TingliangZhang/girlsday2021/image-20210202202509346.png

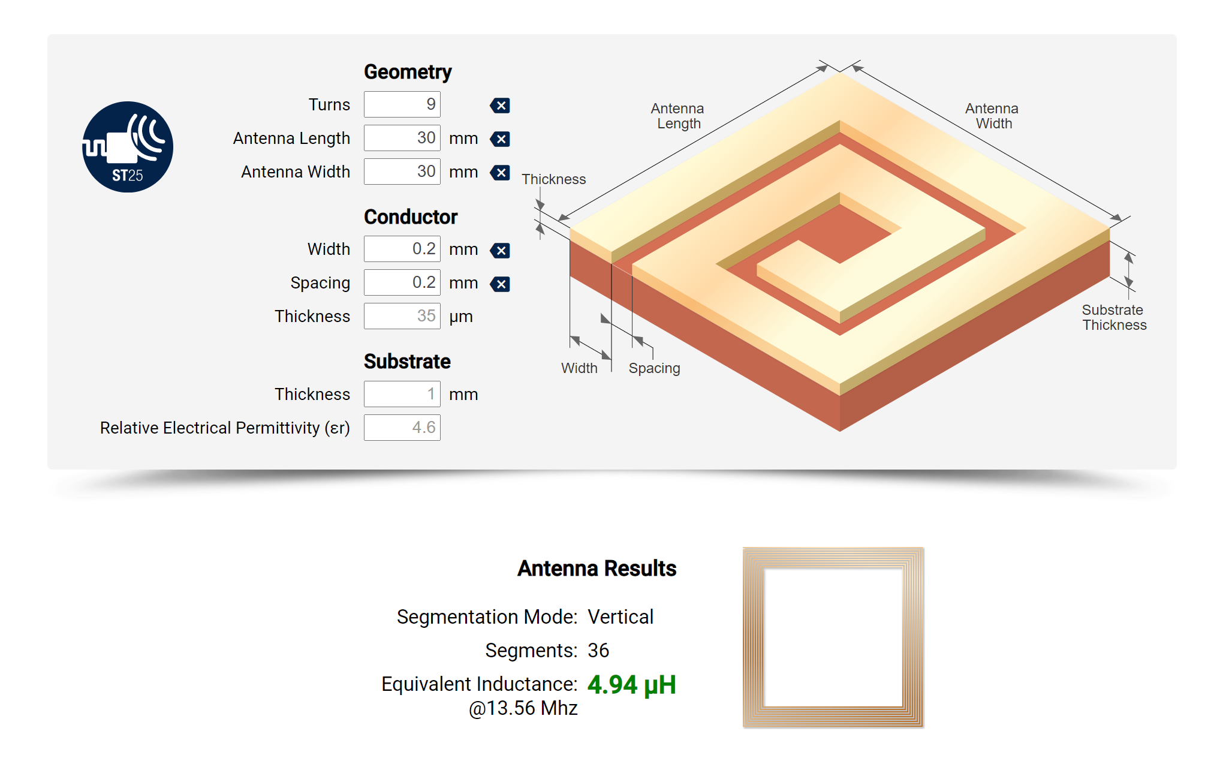
image-20210202202509346.png
